Elecrow-RD/CrowPanel-Advance-5-HMI-ESP32-S3-AI-Powered-IPS-Touch-Screen-800x480/example/V1.0/example_code5.0/lesson-04/README.md

# **Use an SD card to store and display pictures on the device example**

In this case, images are stored on an SD card and displayed on the Advanced AI screen.

***\*Note: All examples run on ESP32 version 3.0.2.\****

### **How to use example**

After opening the sample code in the relevant code file with Arduino IDE.set the required configuration parameters and program it onto the development board

***\*Configuration parameter：\****

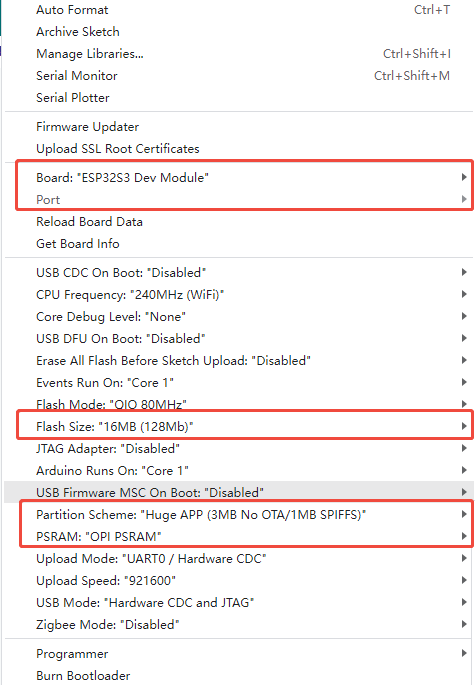
[picture p1: example/V1.0/example_code5.0/lesson-04/4-1.png]


**Note**:Before burning the code, be sure to set the switch on the back of the product to TF Card mode(1 0).

### **How to add Arduino libraries**

Replace the libraries file with the following path:

C:\Users\user name\Documents\Arduio\libraries

***\*Note\****: The 'user name' here is the same as the user computer account name.

## **Documentation tutorial link**：

https://www.elecrow.com/pub/wiki/4.3_4_SD_card_stores_images_and_displays_them_locally.html

## **Video** **tutorial link**：

https://www.youtube.com/watch?v=qSlhvBrq0_w&list=PLwh4PlcPx2Gfrtm7TmlARyF4ccTmIy-gK&index=4
