Elecrow-RD/CrowPanel-Advance-5-HMI-ESP32-S3-AI-Powered-IPS-Touch-Screen-800x480/example/V1.2_and_V1.3/IDF_Code/Lesson03-LVGL_Control_LED/components/lvgl__lvgl/docs/_static/img/js_on_device.jpg

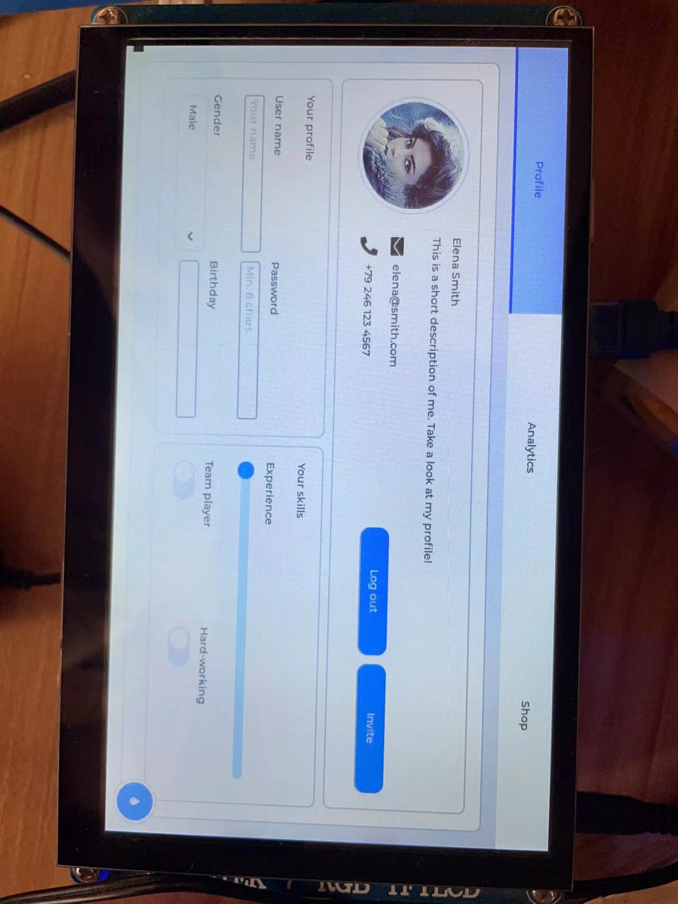
example/V1.2_and_V1.3/IDF_Code/Lesson03-LVGL_Control_LED/components/lvgl__lvgl/docs/_static/img/js_on_device.jpg
