Elecrow-RD/CrowPanel-Advance-5-HMI-ESP32-S3-AI-Powered-IPS-Touch-Screen-800x480/example/V1.2_and_V1.3/IDF_Code/Lesson04_DHT_screen_4.3_5.0_7.0/components/lvgl__lvgl/docs/misc/perfetto_ui.png

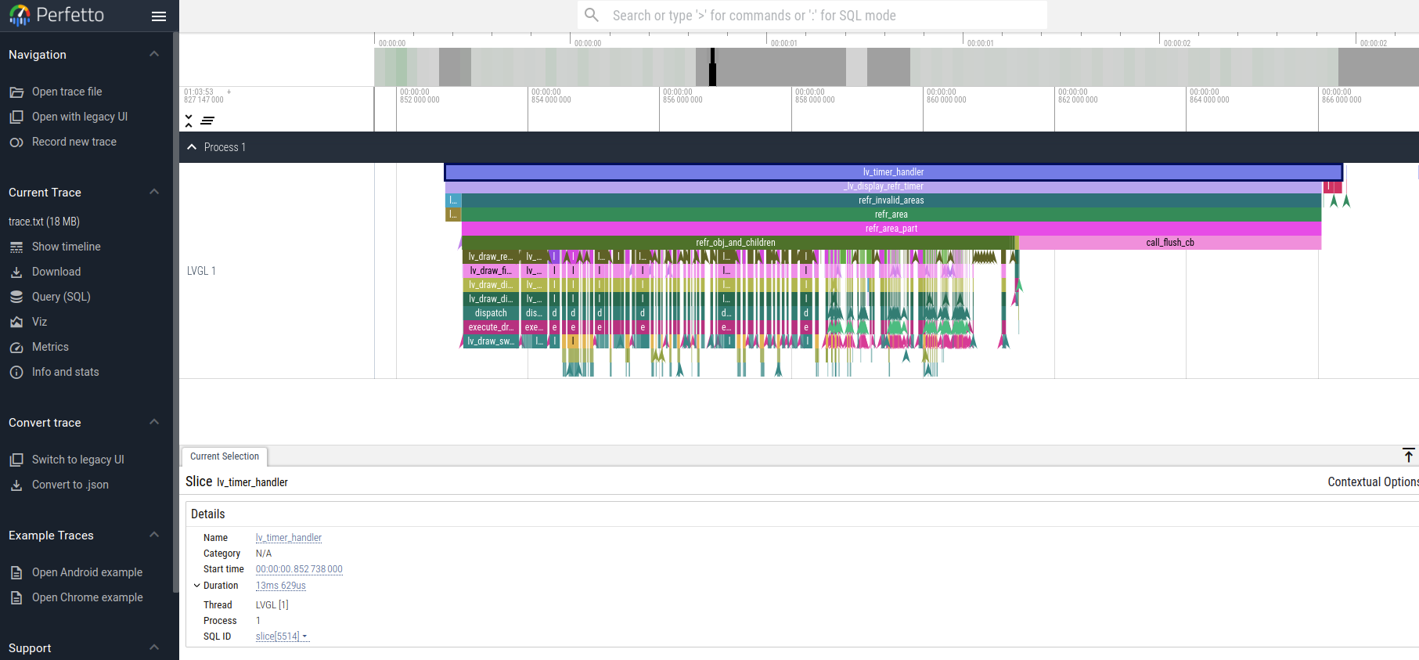
example/V1.2_and_V1.3/IDF_Code/Lesson04_DHT_screen_4.3_5.0_7.0/components/lvgl__lvgl/docs/misc/perfetto_ui.png
