Elecrow-RD/CrowPanel-Advance-5-HMI-ESP32-S3-AI-Powered-IPS-Touch-Screen-800x480/example/V1.2_and_V1.3/Arduino/lesson-04/LovyanGFX/examples_for_PC/images/vs_build.png

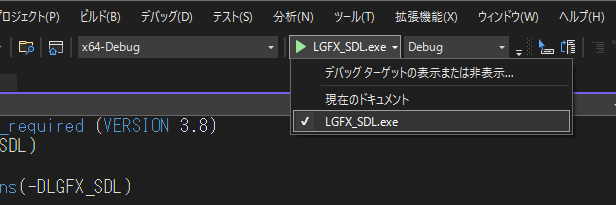
example/V1.2_and_V1.3/Arduino/lesson-04/LovyanGFX/examples_for_PC/images/vs_build.png
